dogman1214/keeboard/Image Gallery/1.jpg

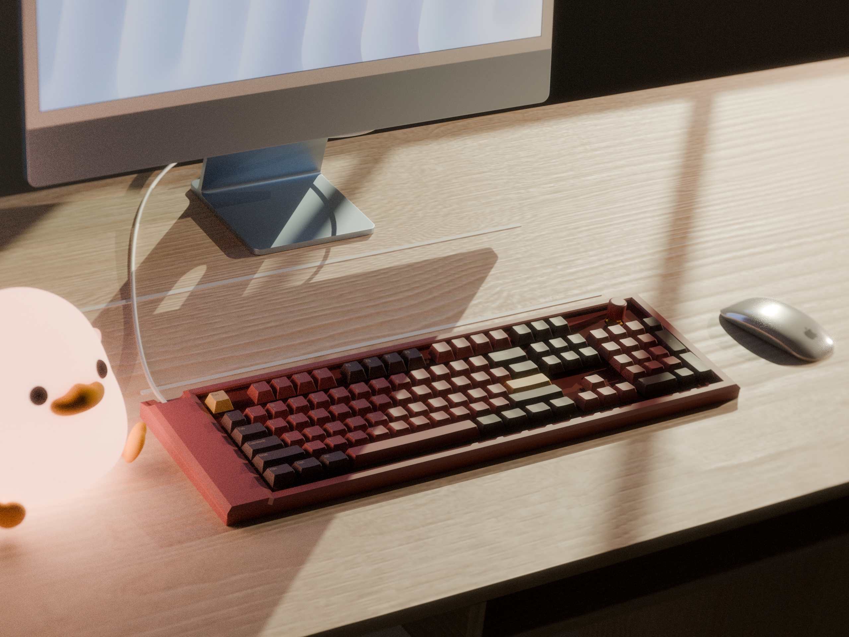
Image Gallery/1.jpg
