dogman1214/keeboard/Image Gallery/2_1.jpg

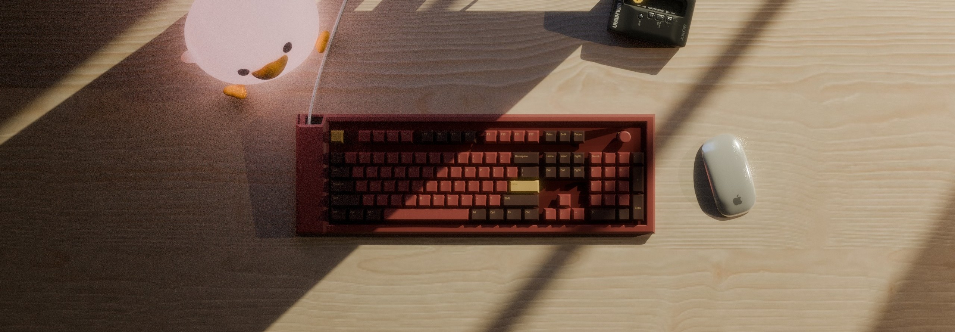
Image Gallery/2_1.jpg
