dogman1214/keeboard/Image Gallery/2.jpg

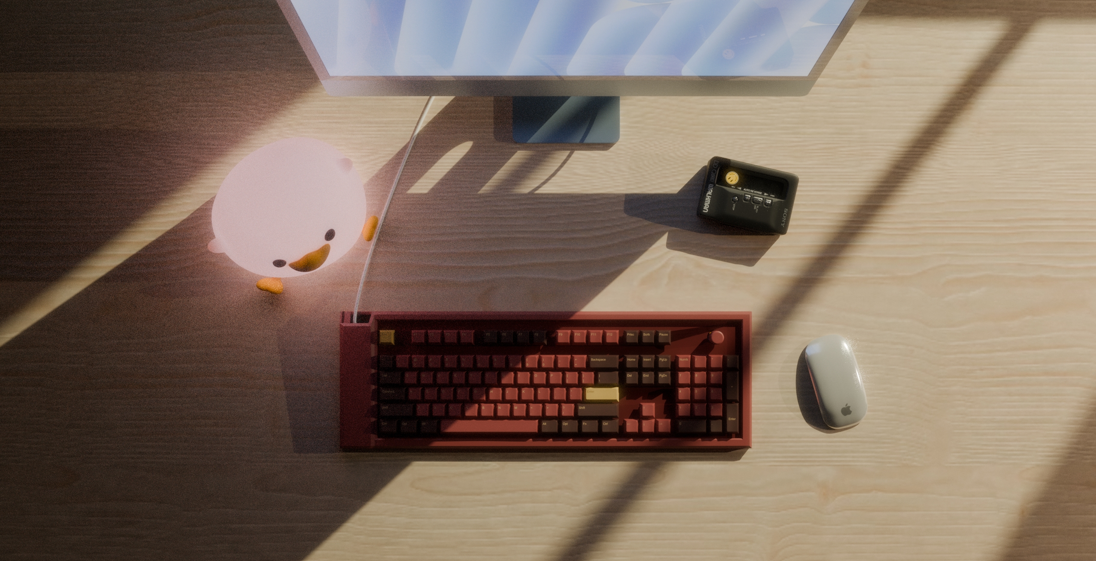
Image Gallery/2.jpg
