dogman1214/keeboard/Image Gallery/Screenshot 2026-09-18 212607.png

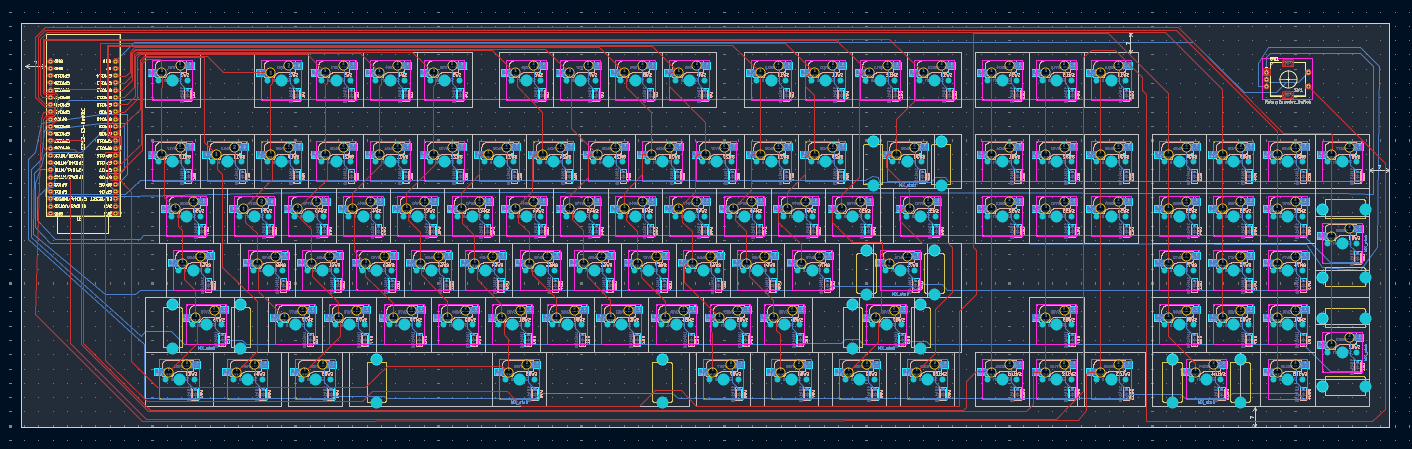
Image Gallery/Screenshot 2026-09-18 212607.png
