dogman1214/keeboard/FIRMWARE/rmk/rmk-config/src/resolved/build_constants.rs

use serde::Deserialize;

use crate::{DEFAULT_PASSKEY_ENTRY_TIMEOUT_SECS, MIN_PASSKEY_ENTRY_TIMEOUT_SECS};

const SUBSCRIBER_DEFAULT_CONFIG: &str = include_str!("../default_config/subscriber_default.toml");

/// Parsed representation of `subscriber_default.toml`.
#[derive(Deserialize)]
struct SubscriberConfig {
    subscriber: Vec<SubscriberEntry>,
}

/// A single entry: bump `subs` for each listed event when all `features` are enabled.
#[derive(Deserialize)]
struct SubscriberEntry {
    features: Vec<String>,
    events: Vec<SubscriberEventEntry>,
}

/// Per-event subscriber bump. `count` defaults to 1.
#[derive(Deserialize)]
struct SubscriberEventEntry {
    name: String,
    #[serde(default = "default_sub_count")]
    count: usize,
}

fn default_sub_count() -> usize {
    1
}

/// Compile-time constants emitted as `pub const` items by `rmk-types/build.rs`.
pub struct BuildConstants {
    pub combo_max_num: usize,
    pub combo_max_length: usize,
    pub fork_max_num: usize,
    pub morse_max_num: usize,
    pub morse_profile_max_num: usize,
    pub max_patterns_per_key: usize,
    pub macro_space_size: usize,
    pub debounce_time: u16,
    pub mouse_key_interval: u16,
    pub mouse_wheel_interval: u16,
    pub report_channel_size: usize,
    pub vial_channel_size: usize,
    pub flash_channel_size: usize,
    pub split_peripherals_num: usize,
    pub central_battery_user_description: String,
    pub split_battery_peripheral_ids: Vec<usize>,
    pub split_battery_peripheral_user_descriptions: Vec<String>,
    pub ble_profiles_num: usize,
    pub split_central_sleep_timeout_seconds: u32,
    pub protocol_macro_chunk_size: usize,
    pub auto_mouse_layer_max_num: usize,
    /// Rynk RX/TX buffer size (bytes).
    pub rynk_buffer_size: usize,
    pub dongle_pairing_window_secs: u32,
    pub events: Vec<EventChannel>,
    pub passkey: Option<Passkey>,
}

pub struct EventChannel {
    pub name: String,
    pub channel_size: usize,
    pub pubs: usize,
    pub subs: usize,
}

pub struct Passkey {
    pub enabled: bool,
    pub timeout_secs: u32,
}

impl crate::KeyboardTomlConfig {
    /// Build compile-time constants from the configuration.
    ///
    /// `active_features` contains feature names enabled on the
    /// **downstream crate** (e.g. `["split", "_ble"]`). These are matched
    /// against `subscriber_default.toml` to auto-bump event subscriber counts.
    pub fn build_constants(&self, active_features: &[&str]) -> Result<BuildConstants, String> {
        let rmk = &self.rmk;

        // Fix split_peripherals_num: when split feature is enabled, ensure at least 1
        let split_peripherals_num = if active_features.contains(&"split") && rmk.split_peripherals_num < 1 {
            1
        } else {
            rmk.split_peripherals_num
        };
        if active_features.contains(&"split")
            && let Some(split) = &self.split
        {
            for (id, peripheral) in split.peripheral.iter().enumerate() {
                if peripheral.battery_user_description.is_some() && peripheral.battery_adc_pin.is_none() {
                    return Err(format!(
                        "keyboard.toml: [[split.peripheral]] at index {id} requires battery_adc_pin when battery_user_description is set"
                    ));
                }
            }
        }
        let split_battery_peripheral_ids = if active_features.contains(&"split") {
            match &self.split {
                Some(split) => split
                    .peripheral
                    .iter()
                    .enumerate()
                    .filter_map(|(id, peripheral)| peripheral.battery_adc_pin.as_ref().map(|_| id))
                    .collect(),
                None => Vec::new(),
            }
        } else {
            Vec::new()
        };
        let central_battery_user_description = self
            .split
            .as_ref()
            .and_then(|split| split.central.battery_user_description.clone())
            .or_else(|| self.ble.as_ref().and_then(|ble| ble.battery_user_description.clone()))
            .unwrap_or_else(|| "Central".to_string());
        let split_battery_peripheral_user_descriptions = split_battery_peripheral_ids
            .iter()
            .map(|id| {
                self.split
                    .as_ref()
                    .and_then(|split| split.peripheral.get(*id))
                    .and_then(|peripheral| peripheral.battery_user_description.clone())
                    .unwrap_or_else(|| format!("Peripheral {id}"))
            })
            .collect();
        // Build event channels
        macro_rules! event_channels {
            ($($field:ident),* $(,)?) => {
                vec![$(
                    EventChannel {
                        name: stringify!($field).to_string(),
                        channel_size: self.event.$field.channel_size,
                        pubs: self.event.$field.pubs,
                        subs: self.event.$field.subs,
                    },
                )*]
            };
        }

        let mut events = event_channels!(
            connection_status_change,
            modifier,
            keyboard,
            layer_change,
            wpm_update,
            led_indicator,
            sleep_state,
            battery_status,
            battery_adc,
            charging_state,
            pointing,
            peripheral_connected,
            central_connected,
            peripheral_battery,
            clear_peer,
            dongle_state,
            dfu_status,
            action,
        );

        // Auto-bump subscriber counts based on enabled feature flags.
        // Declarations live in subscriber_default.toml.
        apply_feature_subscriber_bumps(&mut events, active_features);
        if !split_battery_peripheral_ids.is_empty()
            && active_features.contains(&"split")
            && active_features.contains(&"_ble")
            && let Some(event) = events.iter_mut().find(|event| event.name == "peripheral_battery")
        {
            event.subs += 1;
        }

        // Only validate passkey settings when the build will emit passkey constants.
        let passkey = if active_features.contains(&"passkey_entry") {
            self.ble.as_ref().map(resolve_passkey_enabled).transpose()?
        } else {
            None
        };

        // Validate that config values do not exceed protocol ceilings.
        use crate::protocol_limits;
        if rmk.combo_max_length > protocol_limits::MAX_COMBO_SIZE {
            return Err(format!(
                "combo_max_length ({}) exceeds protocol ceiling MAX_COMBO_SIZE ({})",
                rmk.combo_max_length,
                protocol_limits::MAX_COMBO_SIZE
            ));
        }
        if rmk.max_patterns_per_key > protocol_limits::MAX_MORSE_SIZE {
            return Err(format!(
                "max_patterns_per_key ({}) exceeds protocol ceiling MAX_MORSE_SIZE ({})",
                rmk.max_patterns_per_key,
                protocol_limits::MAX_MORSE_SIZE
            ));
        }
        if rmk.protocol_macro_chunk_size > protocol_limits::MAX_MACRO_DATA_SIZE {
            return Err(format!(
                "protocol_macro_chunk_size ({}) exceeds protocol ceiling MAX_MACRO_DATA_SIZE ({})",
                rmk.protocol_macro_chunk_size,
                protocol_limits::MAX_MACRO_DATA_SIZE
            ));
        }
        let auto_mouse_layer_max_num = rmk
            .auto_mouse_layer_max_num
            .unwrap_or(crate::resolved::behavior::DEFAULT_AUTO_MOUSE_LAYER_MAX_NUM);
        if let Some(entries) = self.behavior.as_ref().and_then(|b| b.auto_mouse_layer.as_ref()) {
            if entries.len() > auto_mouse_layer_max_num {
                return Err(format!(
                    "number of [[behavior.auto_mouse_layer]] entries ({}) exceeds auto_mouse_layer_max_num ({})",
                    entries.len(),
                    auto_mouse_layer_max_num
                ));
            }
            let uses_action_event = entries
                .iter()
                .any(|e| e.deactivate_on_key == Some(true) || e.reset_timeout_on_key == Some(true));
            if uses_action_event && events.iter().any(|e| e.name == "action" && e.subs == 0) {
                return Err(
                    "[[behavior.auto_mouse_layer]].deactivate_on_key / reset_timeout_on_key require [event.action] subs to be at least 1".to_string(),
                );
            }
        }

        // Host capability fields are u8/u16 on the wire; check the values no deserializer bound
        // covers (morse_max_num and split_peripherals_num can also be auto-raised past 255).
        validate_u8_capability("morse_max_num", rmk.morse_max_num)?;
        validate_u8_capability("split_peripherals_num", split_peripherals_num)?;
        validate_u8_capability("ble_profiles_num", rmk.ble_profiles_num)?;
        validate_u16_capability("macro_space_size", rmk.macro_space_size)?;
        validate_u16_capability("rynk_buffer_size", rmk.rynk_buffer_size)?;
        Ok(BuildConstants {
            combo_max_num: rmk.combo_max_num,
            combo_max_length: rmk.combo_max_length,
            fork_max_num: rmk.fork_max_num,
            morse_max_num: rmk.morse_max_num,
            morse_profile_max_num: rmk.morse_profile_max_num,
            max_patterns_per_key: rmk.max_patterns_per_key,
            macro_space_size: rmk.macro_space_size,
            debounce_time: rmk.debounce_time,
            mouse_key_interval: rmk.mouse_key_interval,
            mouse_wheel_interval: rmk.mouse_wheel_interval,
            report_channel_size: rmk.report_channel_size,
            vial_channel_size: rmk.vial_channel_size,
            flash_channel_size: rmk.flash_channel_size,
            split_peripherals_num,
            central_battery_user_description,
            split_battery_peripheral_ids,
            split_battery_peripheral_user_descriptions,
            ble_profiles_num: rmk.ble_profiles_num,
            split_central_sleep_timeout_seconds: rmk.split_central_sleep_timeout_seconds,
            protocol_macro_chunk_size: rmk.protocol_macro_chunk_size,
            auto_mouse_layer_max_num,
            rynk_buffer_size: rmk.rynk_buffer_size,
            dongle_pairing_window_secs: rmk.dongle_pairing_window_secs,
            events,
            passkey,
        })
    }
}

fn validate_u8_capability(name: &str, value: usize) -> Result<(), String> {
    if value > u8::MAX as usize {
        return Err(format!(
            "{name} ({value}) exceeds the u8 host capability field (max 255)"
        ));
    }
    Ok(())
}

fn validate_u16_capability(name: &str, value: usize) -> Result<(), String> {
    if value > u16::MAX as usize {
        return Err(format!(
            "{name} ({value}) exceeds the u16 host capability field (max 65535)"
        ));
    }
    Ok(())
}

/// Bump event subscriber counts based on feature flags declared in `subscriber_default.toml`.
///
/// `active_features` contains lowercase feature names (e.g. `"split"`, `"_ble"`).
fn apply_feature_subscriber_bumps(events: &mut [EventChannel], active_features: &[&str]) {
    let sub_config: SubscriberConfig =
        toml::from_str(SUBSCRIBER_DEFAULT_CONFIG).expect("Failed to parse subscriber_default.toml");

    for entry in &sub_config.subscriber {
        let all_enabled = entry.features.iter().all(|f| active_features.contains(&f.as_str()));
        if all_enabled {
            for sub_event in &entry.events {
                if let Some(event) = events.iter_mut().find(|e| e.name == sub_event.name) {
                    event.subs += sub_event.count;
                } else {
                    println!(
                        "cargo:warning=subscriber_default.toml: unknown event \"{}\"",
                        sub_event.name
                    );
                }
            }
        }
    }
}

fn resolve_passkey_enabled(ble: &crate::BleConfig) -> Result<Passkey, String> {
    let enabled = ble.passkey_entry.unwrap_or(false);
    let timeout_secs = ble.passkey_entry_timeout.unwrap_or(DEFAULT_PASSKEY_ENTRY_TIMEOUT_SECS);
    if timeout_secs < MIN_PASSKEY_ENTRY_TIMEOUT_SECS {
        return Err(format!(
            "keyboard.toml: [ble.passkey_entry_timeout] must be at least {} seconds, got {}",
            MIN_PASSKEY_ENTRY_TIMEOUT_SECS, timeout_secs
        ));
    }
    Ok(Passkey { enabled, timeout_secs })
}

#[cfg(test)]
mod tests {
    use super::{BuildConstants, resolve_passkey_enabled, validate_u8_capability, validate_u16_capability};
    use crate::{
        BleConfig, DEFAULT_PASSKEY_ENTRY_TIMEOUT_SECS, KeyboardTomlConfig, MIN_PASSKEY_ENTRY_TIMEOUT_SECS,
        SplitBoardConfig, SplitConfig,
    };

    #[test]
    fn reserves_led_subscribers_for_display_split_and_dual_rynk_sessions() {
        let config: KeyboardTomlConfig = toml::from_str("").unwrap();
        let constants = config.build_constants(&["display", "split", "rynk", "_ble"]).unwrap();
        let led_indicator = constants
            .events
            .iter()
            .find(|event| event.name == "led_indicator")
            .unwrap();

        // Three indicator processors, the display, two split peripherals, and USB/BLE Rynk sessions.
        assert_eq!(led_indicator.subs, 8);
    }

    #[test]
    fn dongle_display_reserves_the_dongle_state_subscriber() {
        let config: KeyboardTomlConfig = toml::from_str("").unwrap();
        let subs = |features: &[&str]| {
            config
                .build_constants(features)
                .unwrap()
                .events
                .into_iter()
                .find(|event| event.name == "dongle_state")
                .unwrap()
                .subs
        };

        // Nobody listens on a screenless dongle, so publishing there is a no-op.
        assert_eq!(subs(&["dongle", "_ble", "storage"]), 0);
        assert_eq!(subs(&["dongle", "display", "_ble", "storage"]), 1);
    }

    #[test]
    fn configless_split_has_no_battery_peripheral_ids() {
        let config: KeyboardTomlConfig = toml::from_str("").unwrap();

        let constants = config.build_constants(&["split", "_ble"]).unwrap();

        assert!(constants.split_battery_peripheral_ids.is_empty());
        assert!(constants.split_battery_peripheral_user_descriptions.is_empty());
    }

    #[test]
    fn split_ble_reserves_peripheral_battery_subscriber_only_with_battery_ids() {
        let mut config: KeyboardTomlConfig = toml::from_str("").unwrap();
        config.split = Some(SplitConfig {
            peripheral: vec![SplitBoardConfig {
                battery_adc_pin: Some("P0_02".to_string()),
                ..Default::default()
            }],
            ..Default::default()
        });
        config.auto_calculate_parameters();

        let base = config.build_constants(&[]).unwrap();
        let split_ble = config.build_constants(&["split", "_ble"]).unwrap();
        let subs = |constants: &BuildConstants| {
            constants
                .events
                .iter()
                .find(|event| event.name == "peripheral_battery")
                .unwrap()
                .subs
        };

        assert_eq!(subs(&split_ble), subs(&base) + 1);
    }

    #[test]
    fn resolves_split_battery_peripheral_ids() {
        let mut config: KeyboardTomlConfig = toml::from_str("").unwrap();
        config.split = Some(SplitConfig {
            peripheral: vec![
                SplitBoardConfig {
                    battery_adc_pin: Some("P0_02".to_string()),
                    ..Default::default()
                },
                SplitBoardConfig::default(),
                SplitBoardConfig {
                    battery_adc_pin: Some("P0_04".to_string()),
                    ..Default::default()
                },
            ],
            ..Default::default()
        });
        config.auto_calculate_parameters();

        let constants = config.build_constants(&["split", "_ble"]).unwrap();

        assert_eq!(constants.split_battery_peripheral_ids, [0, 2]);
    }

    #[test]
    fn split_with_battery_ids_uses_zero_based_peripheral_ids() {
        let mut config: KeyboardTomlConfig = toml::from_str("").unwrap();
        config.split = Some(SplitConfig {
            peripheral: vec![
                SplitBoardConfig::default(),
                SplitBoardConfig {
                    battery_adc_pin: Some("P0_02".to_string()),
                    ..Default::default()
                },
            ],
            ..Default::default()
        });
        config.auto_calculate_parameters();

        let constants = config.build_constants(&["split"]).unwrap();

        assert_eq!(constants.split_battery_peripheral_ids, [1]);
        assert_eq!(constants.split_battery_peripheral_user_descriptions, ["Peripheral 1"]);
    }

    #[test]
    fn split_without_battery_ids_does_not_reserve_peripheral_battery_subscriber() {
        let mut config: KeyboardTomlConfig = toml::from_str("").unwrap();
        config.split = Some(SplitConfig {
            peripheral: vec![SplitBoardConfig::default()],
            ..Default::default()
        });
        config.auto_calculate_parameters();

        let base = config.build_constants(&[]).unwrap();
        let split_ble = config.build_constants(&["split", "_ble"]).unwrap();
        let subs = |constants: &BuildConstants| {
            constants
                .events
                .iter()
                .find(|event| event.name == "peripheral_battery")
                .unwrap()
                .subs
        };

        assert_eq!(subs(&split_ble), subs(&base));
    }

    #[test]
    fn non_split_does_not_reserve_peripheral_battery_subscriber() {
        let config: KeyboardTomlConfig = toml::from_str("").unwrap();

        let base = config.build_constants(&[]).unwrap();
        let ble = config.build_constants(&["_ble"]).unwrap();
        let subs = |constants: &BuildConstants| {
            constants
                .events
                .iter()
                .find(|event| event.name == "peripheral_battery")
                .unwrap()
                .subs
        };

        assert!(ble.split_battery_peripheral_ids.is_empty());
        assert_eq!(subs(&ble), subs(&base));
    }

    #[test]
    fn rejects_peripheral_battery_user_description_without_adc_pin() {
        let mut config: KeyboardTomlConfig = toml::from_str("").unwrap();
        config.split = Some(SplitConfig {
            peripheral: vec![SplitBoardConfig {
                battery_user_description: Some("Right".to_string()),
                ..Default::default()
            }],
            ..Default::default()
        });

        assert!(config.build_constants(&[]).is_ok());

        let err = match config.build_constants(&["split"]) {
            Ok(_) => panic!("expected battery user description validation failure"),
            Err(err) => err,
        };

        assert_eq!(
            err,
            "keyboard.toml: [[split.peripheral]] at index 0 requires battery_adc_pin when battery_user_description is set"
        );
    }

    #[test]
    fn resolves_custom_battery_user_descriptions() {
        let mut config: KeyboardTomlConfig = toml::from_str("").unwrap();
        config.ble = Some(BleConfig {
            enabled: true,
            battery_user_description: Some("Fallback Central".to_string()),
            ..Default::default()
        });
        config.split = Some(SplitConfig {
            central: SplitBoardConfig {
                battery_user_description: Some("Left".to_string()),
                ..Default::default()
            },
            peripheral: vec![
                SplitBoardConfig {
                    battery_adc_pin: Some("P0_02".to_string()),
                    battery_user_description: Some("Right".to_string()),
                    ..Default::default()
                },
                SplitBoardConfig {
                    battery_adc_pin: Some("P0_04".to_string()),
                    ..Default::default()
                },
            ],
            ..Default::default()
        });
        config.auto_calculate_parameters();

        let constants = config.build_constants(&["split", "_ble"]).unwrap();

        assert_eq!(constants.central_battery_user_description, "Left");
        assert_eq!(
            constants.split_battery_peripheral_user_descriptions,
            ["Right", "Peripheral 1"]
        );
    }

    #[test]
    fn validates_passkey_timeout() {
        let ble = BleConfig {
            passkey_entry_timeout: Some(MIN_PASSKEY_ENTRY_TIMEOUT_SECS - 1),
            ..Default::default()
        };

        let err = match resolve_passkey_enabled(&ble) {
            Ok(_) => panic!("expected passkey timeout validation failure"),
            Err(err) => err,
        };
        assert_eq!(
            err,
            format!(
                "keyboard.toml: [ble.passkey_entry_timeout] must be at least {} seconds, got {}",
                MIN_PASSKEY_ENTRY_TIMEOUT_SECS,
                MIN_PASSKEY_ENTRY_TIMEOUT_SECS - 1
            )
        );
    }

    #[test]
    fn uses_default_timeout() {
        let ble = BleConfig::default();
        let passkey = resolve_passkey_enabled(&ble).unwrap();

        assert!(!passkey.enabled);
        assert_eq!(passkey.timeout_secs, DEFAULT_PASSKEY_ENTRY_TIMEOUT_SECS);
    }

    fn parse(toml: &str) -> crate::KeyboardTomlConfig {
        toml::from_str(toml).expect("Failed to parse keyboard config")
    }

    #[test]
    fn auto_mouse_layer_max_num_explicitly_too_small_is_rejected() {
        let toml = "[rmk]\nauto_mouse_layer_max_num = 0\n\n[[behavior.auto_mouse_layer]]\ntarget_layer = 1\n";
        let err = match parse(toml).build_constants(&[]) {
            Ok(_) => panic!("expected auto_mouse_layer_max_num validation failure"),
            Err(err) => err,
        };
        assert!(err.contains("auto_mouse_layer_max_num"));
    }

    #[test]
    fn auto_mouse_layer_within_capacity_is_accepted() {
        let toml = "[rmk]\nauto_mouse_layer_max_num = 1\n\n[[behavior.auto_mouse_layer]]\ntarget_layer = 1\nextra_mouse_keys = [\"LCtrl\"]\n";
        assert!(parse(toml).build_constants(&[]).is_ok());
    }

    #[test]
    fn deactivate_on_key_without_action_subs_is_rejected() {
        let toml = "[[behavior.auto_mouse_layer]]\ntarget_layer = 1\ndeactivate_on_key = true\n";
        let err = match parse(toml).build_constants(&[]) {
            Ok(_) => panic!("expected action subs validation failure"),
            Err(err) => err,
        };
        assert!(err.contains("[event.action]"));
    }

    #[test]
    fn deactivate_on_key_with_action_subs_set_is_accepted() {
        let toml = "[event.action]\nchannel_size = 16\npubs = 1\nsubs = 1\n\n[[behavior.auto_mouse_layer]]\ntarget_layer = 1\ndeactivate_on_key = true\n";
        assert!(parse(toml).build_constants(&[]).is_ok());
    }

    #[test]
    fn ble_reserves_advertising_timeout_wake_subscribers() {
        // ble/mod.rs subscribes to KeyboardEvent/PointingEvent when advertising
        // times out, on top of every permanent subscriber. Without a reserved
        // slot that call panics instead of sleeping until the next key press.
        let base = parse("").build_constants(&[]).unwrap();
        let ble = parse("").build_constants(&["_ble"]).unwrap();

        let subs =
            |constants: &BuildConstants, event: &str| constants.events.iter().find(|e| e.name == event).unwrap().subs;
        for event in ["keyboard", "pointing"] {
            assert_eq!(
                subs(&ble, event),
                subs(&base, event) + 1,
                "{event} needs a wake subscriber slot under _ble"
            );
        }
    }

    #[test]
    fn validates_capability_wire_widths() {
        assert!(validate_u8_capability("ble_profiles_num", 255).is_ok());
        assert_eq!(
            validate_u8_capability("ble_profiles_num", 256),
            Err("ble_profiles_num (256) exceeds the u8 host capability field (max 255)".to_string())
        );

        assert!(validate_u16_capability("macro_space_size", 65535).is_ok());
        assert_eq!(
            validate_u16_capability("macro_space_size", 65536),
            Err("macro_space_size (65536) exceeds the u16 host capability field (max 65535)".to_string())
        );
    }
}
